tang-fu/Hollow-Clock-Pro/04lower/Arduino/Hollow-Clock-Pro/data/img/clock.jpg

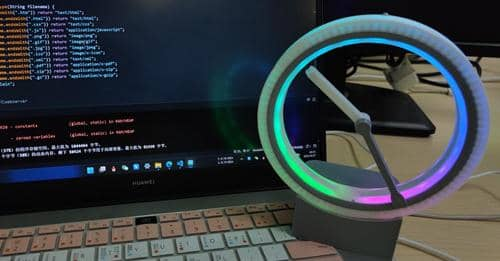
04lower/Arduino/Hollow-Clock-Pro/data/img/clock.jpg
