tang-fu/Hollow-Clock-Pro/02industial_design/3Dmodel/style1/006LED灯罩.stl

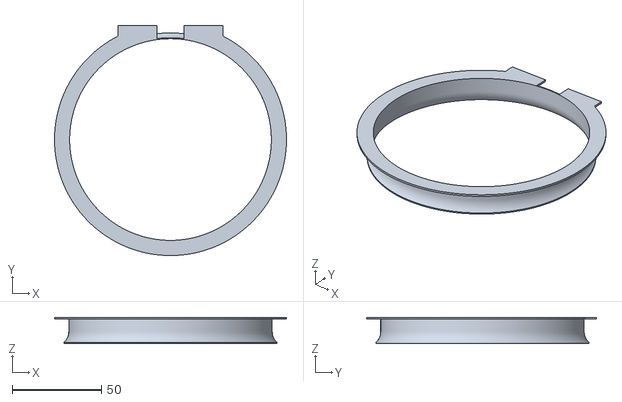
[picture p21: CAD file, 2023-06-22]
02industial_design/3Dmodel/style1/006LED灯罩.stl
130.0 x 128.9 x 14.7
