tang-fu/Hollow-Clock-Pro/02industial_design/3Dmodel/style1/010时针指针.stl

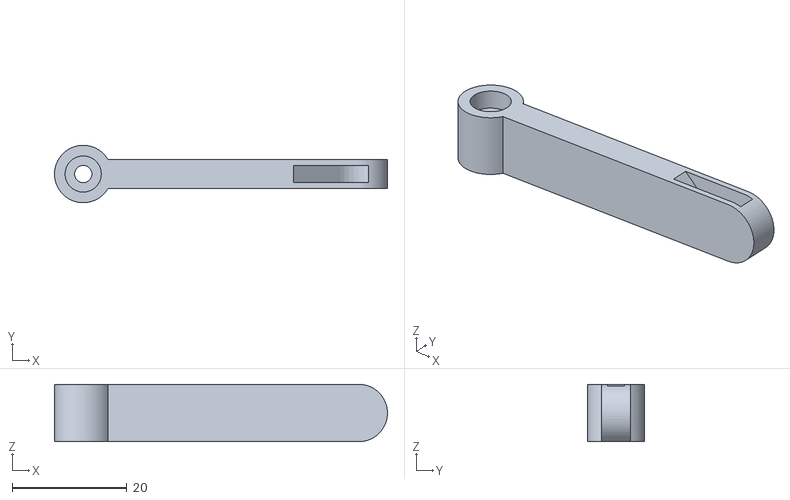
[picture p22: CAD file, 2023-06-22]
02industial_design/3Dmodel/style1/010时针指针.stl
58.0 x 10.0 x 10.0
