tang-fu/Hollow-Clock-Pro/02industial_design/3Dmodel/style1/005后盖.stl

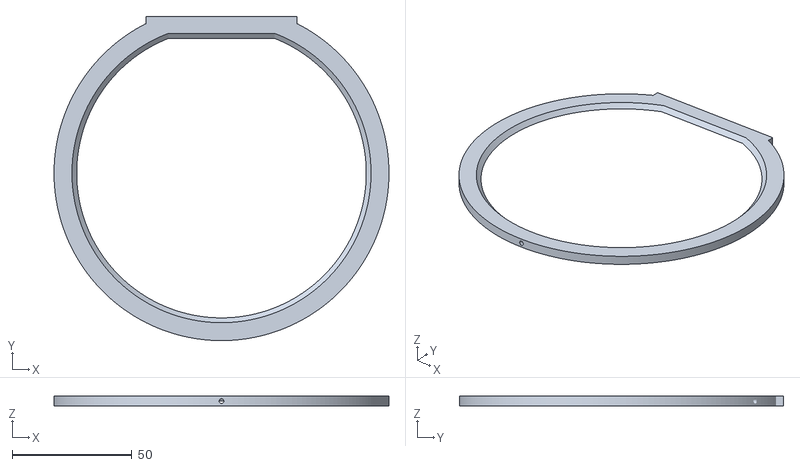
[picture p23: CAD file, 2023-06-22]
02industial_design/3Dmodel/style1/005后盖.stl
140.0 x 135.5 x 4.00
